RootCNC/Root-2-CNC/STL_Files/X Carriage/X Carraige.png

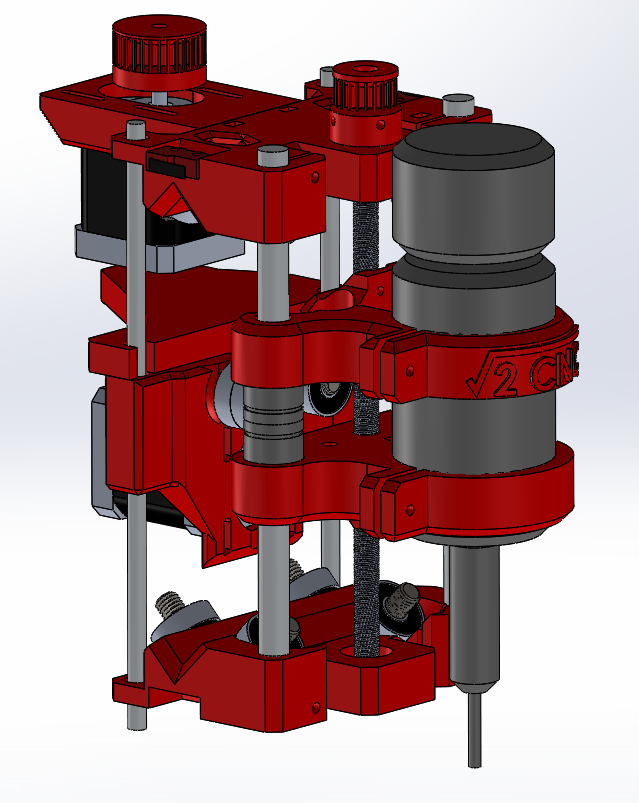
STL_Files/X Carriage/X Carraige.png
