RootCNC/Root-2-CNC/STL_Files/Z Carraige/Spindle Mount.png

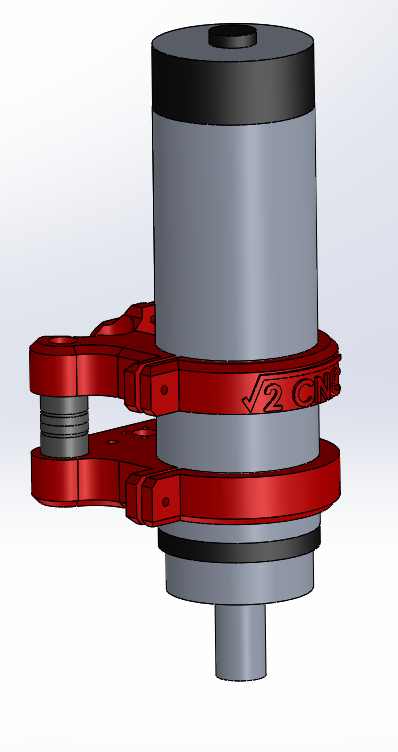
STL_Files/Z Carraige/Spindle Mount.png
