RootCNC/Root-2-CNC/Wooden_Parts/Base Board.png

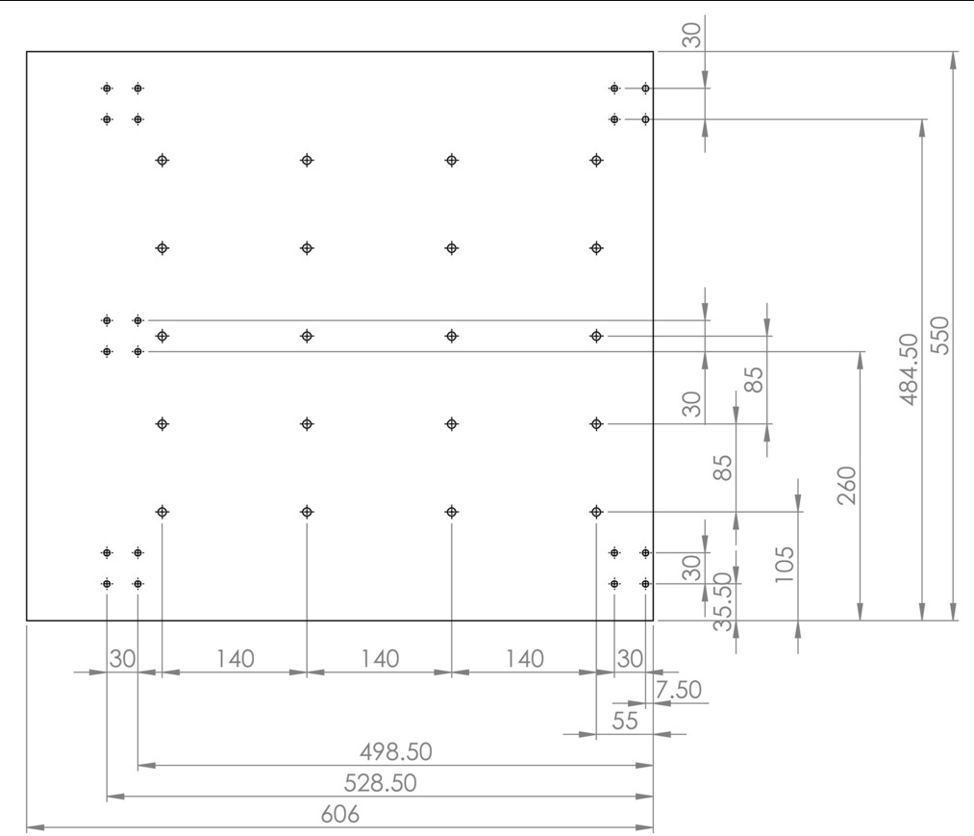
Wooden_Parts/Base Board.png
