RootCNC/Root-2-CNC/Wooden_Parts/Side Panel.png

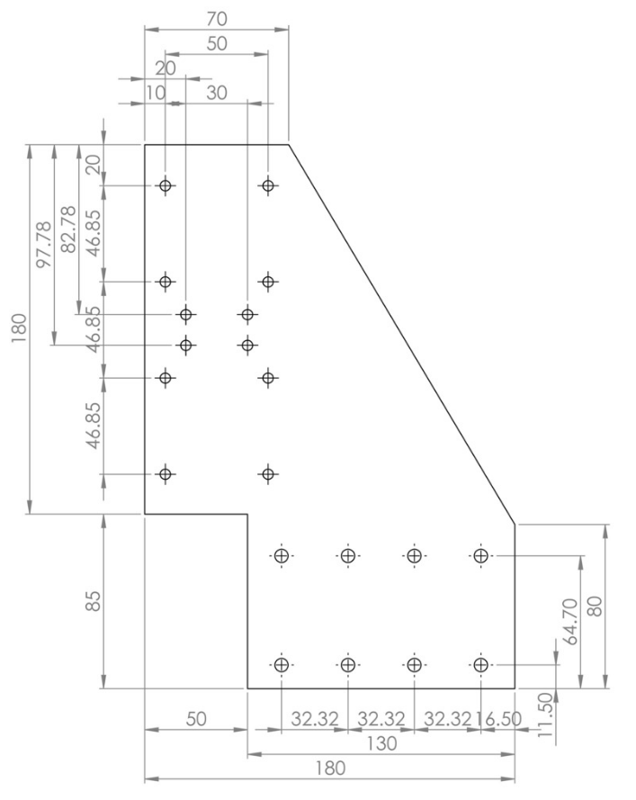
Wooden_Parts/Side Panel.png
