RootCNC/Root-2-CNC/STL_Files/X Carriage/X-Axis Motor Mount.STL

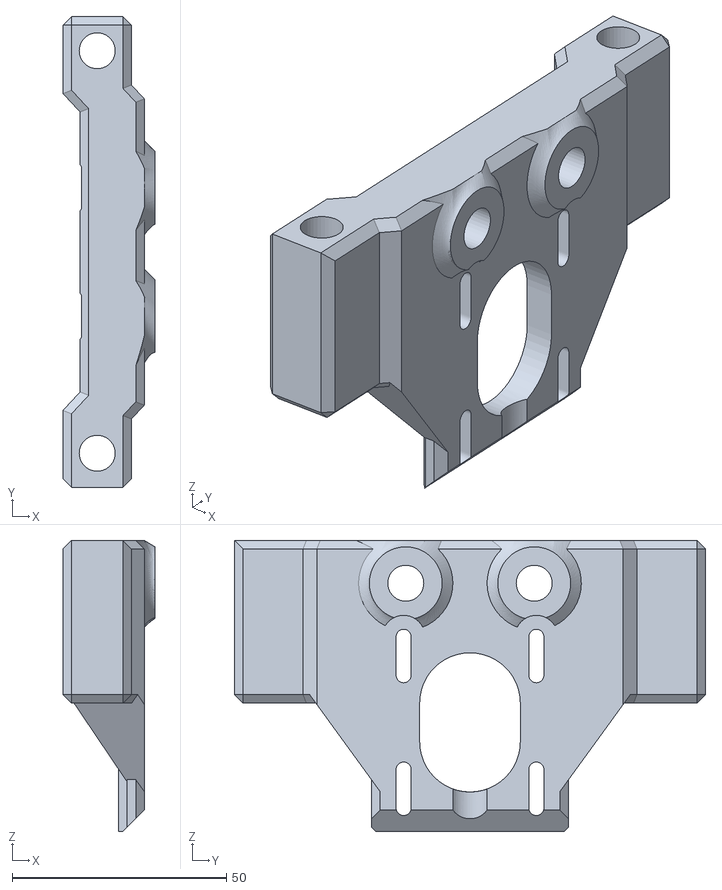
[picture p21: CAD file, 2020-06-19]
STL_Files/X Carriage/X-Axis Motor Mount.STL
21.5 x 110.0 x 68.0
