RootCNC/Root-2-CNC/STL_Files/Y Gantry/X-Axis Belt Clamp.STL

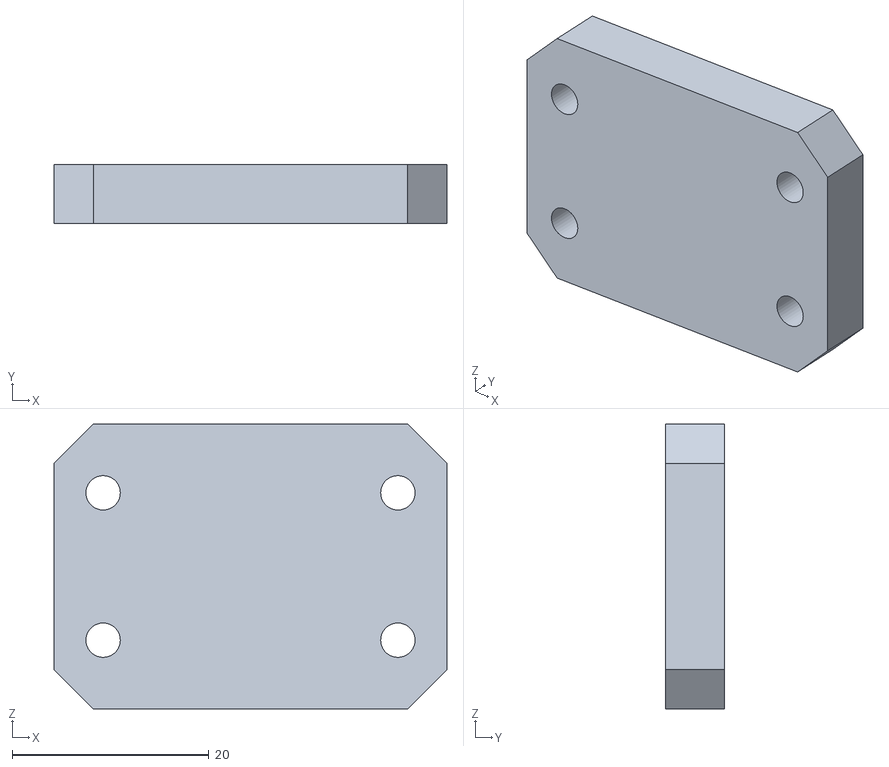
[picture p22: CAD file, 2020-06-19]
STL_Files/Y Gantry/X-Axis Belt Clamp.STL
40.0 x 6.00 x 29.0
