RootCNC/Root-2-CNC/STL_Files/Y Motion/Foot.STL

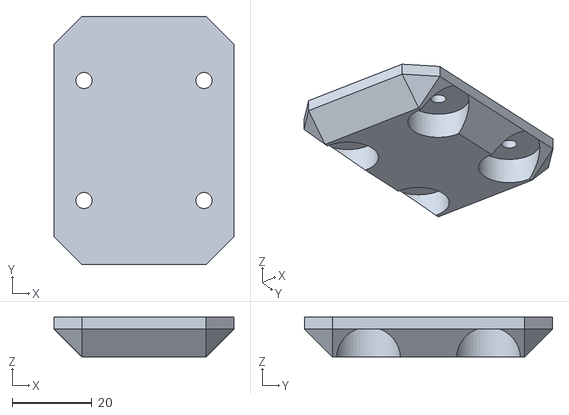
[picture p23: CAD file, 2020-06-19]
STL_Files/Y Motion/Foot.STL
45.0 x 62.0 x 10.0
