RootCNC/Root-2-CNC/STL_Files/Y Motion/INCHES 1'/Root 2 CNC - Base and Y axis assm-1 Y-Axis Bar Mount Idler INCHES.STL

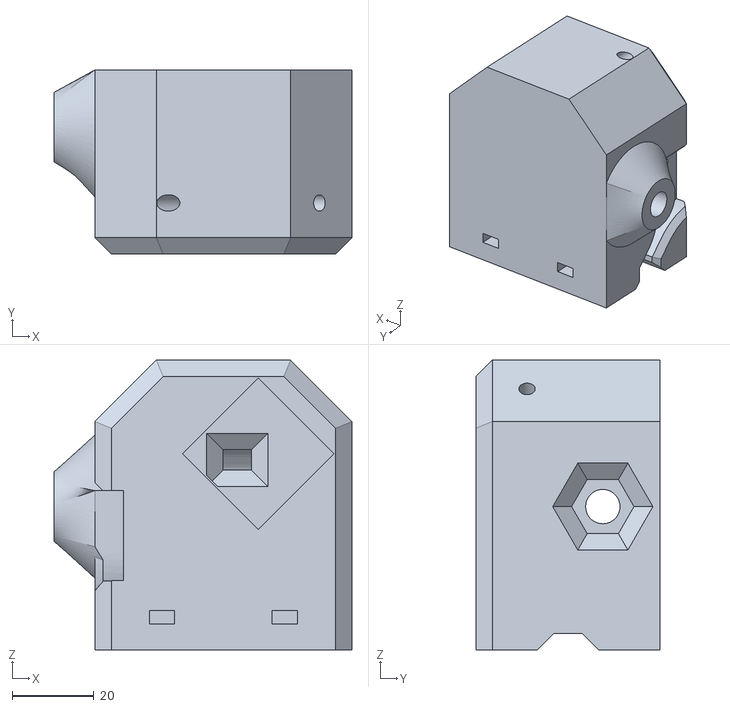
[picture p24: CAD file, 2020-06-19]
STL_Files/Y Motion/INCHES 1'/Root 2 CNC - Base and Y axis assm-1 Y-Axis Bar Mount Idler INCHES.STL
72.8 x 45.0 x 70.8
