RootCNC/Root-2-CNC/STL_Files/Z Carraige/52mm/Spindle Clamp 52mm Top.STL

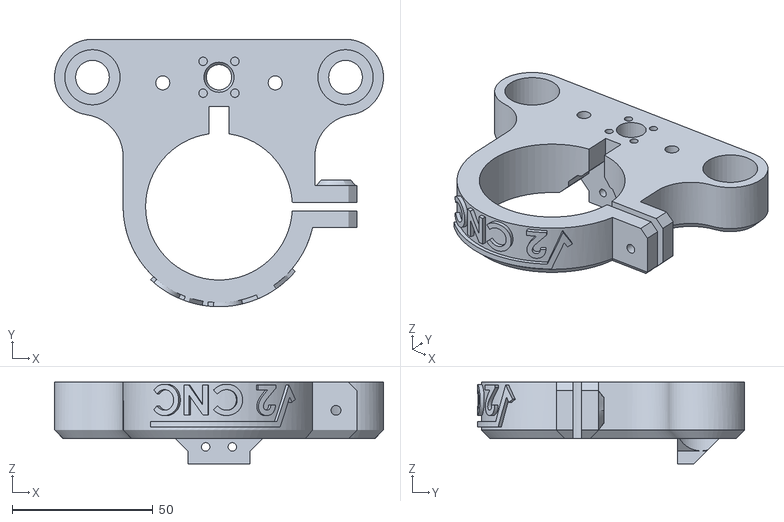
[picture p25: CAD file, 2020-06-19]
STL_Files/Z Carraige/52mm/Spindle Clamp 52mm Top.STL
117.0 x 95.1 x 29.0
