RootCNC/Root-2-CNC/STL_Files/Z Carraige/80mm/Spindle Clamp 80mm Bottom.STL

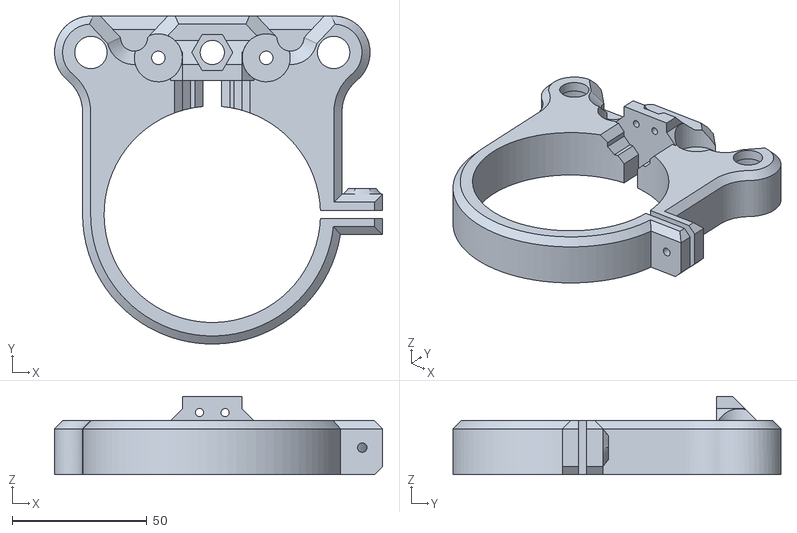
[picture p26: CAD file, 2020-06-19]
STL_Files/Z Carraige/80mm/Spindle Clamp 80mm Bottom.STL
121.6 x 121.6 x 29.0
