RootCNC/Root-2-CNC/Wooden_Parts/X-Axis Side Pannel (Wood).STL

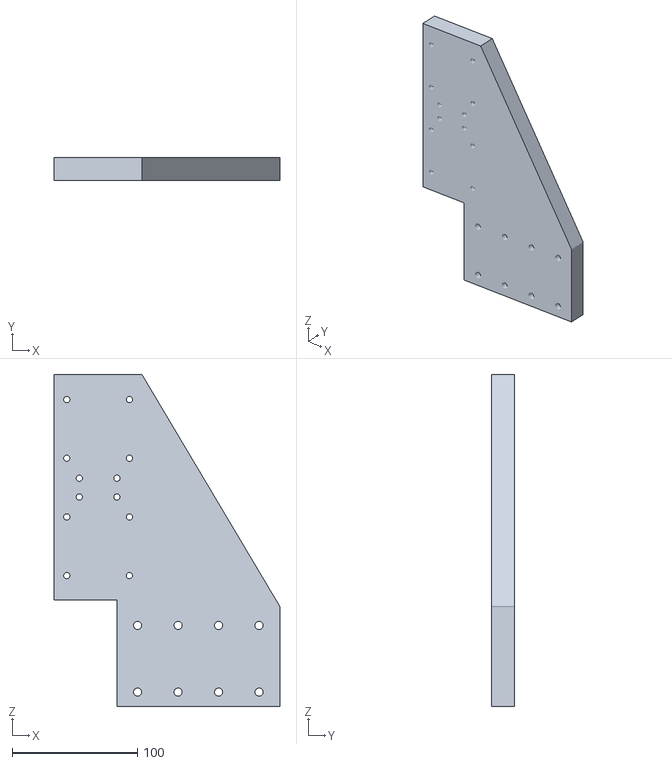
[picture p27: CAD file, 2020-06-19]
Wooden_Parts/X-Axis Side Pannel (Wood).STL
180.0 x 18.0 x 265.0
