RootCNC/Root-2-CNC/STL_Files/X Carriage/X-Axis Carriage Drag Chain Mount Idler.STL

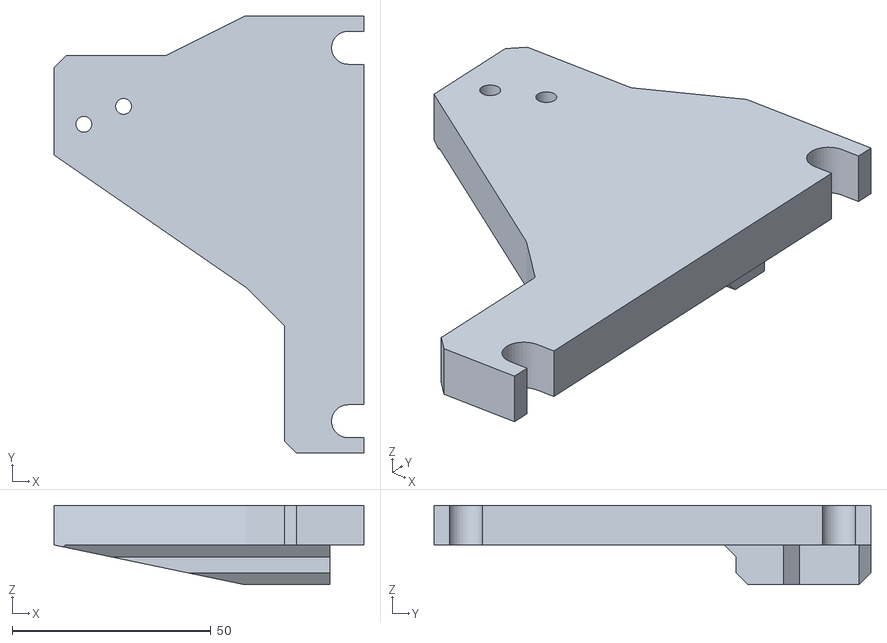
[picture p28: CAD file, 2020-06-19]
STL_Files/X Carriage/X-Axis Carriage Drag Chain Mount Idler.STL
78.0 x 110.0 x 20.0
