RootCNC/Root-2-CNC/STL_Files/Y Gantry/Y-Axis Belt Clamp GT2.STL

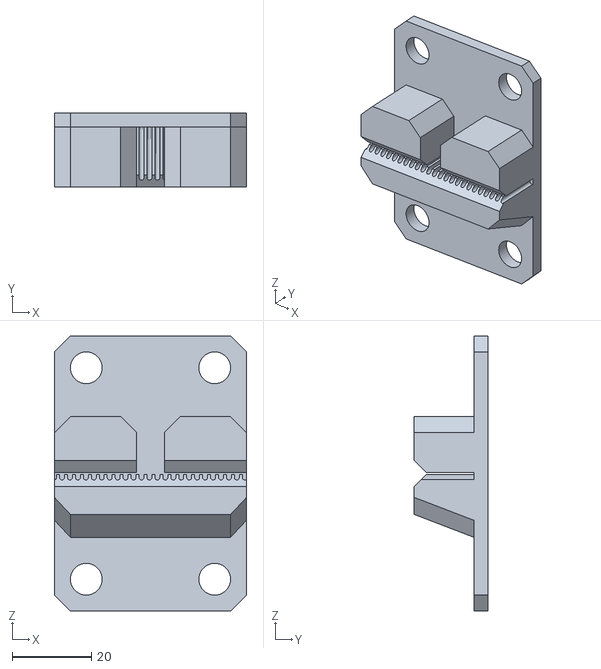
[picture p29: CAD file, 2020-06-19]
STL_Files/Y Gantry/Y-Axis Belt Clamp GT2.STL
48.3 x 18.5 x 69.2
