RootCNC/Root-2-CNC/STL_Files/Y Motion/Y-Axis Motor Mount Mirror.STL

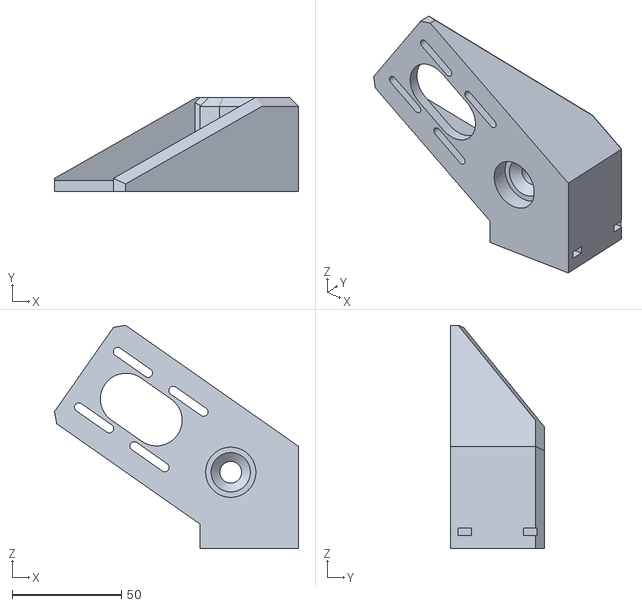
[picture p30: CAD file, 2020-06-19]
STL_Files/Y Motion/Y-Axis Motor Mount Mirror.STL
111.6 x 43.0 x 102.3
