RootCNC/Root-2-CNC/STL_Files/X Carriage/3M Pulley 32T 5mm.STL

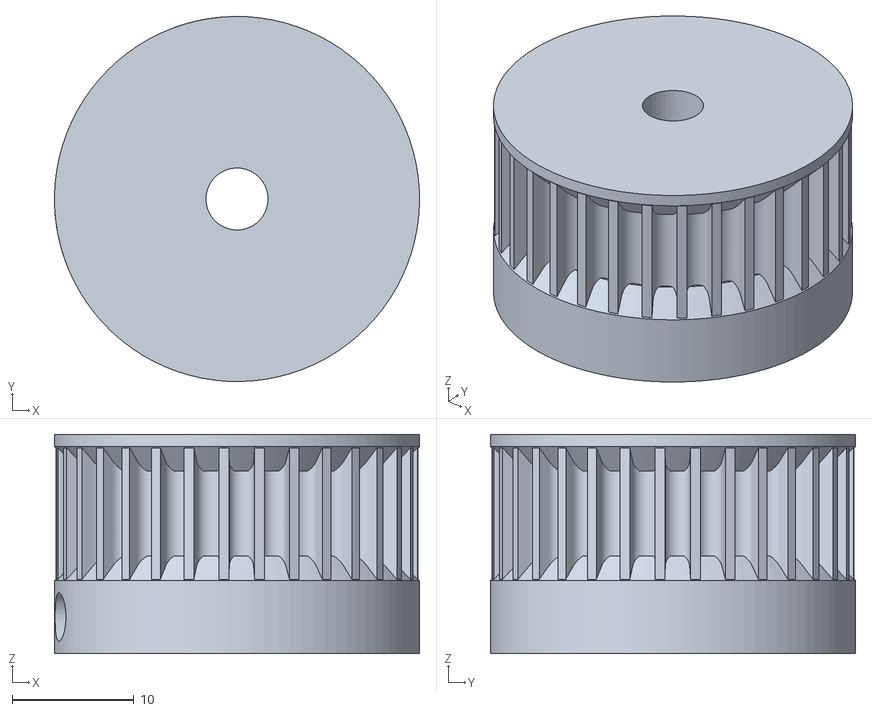
[picture p31: CAD file, 2020-06-19]
STL_Files/X Carriage/3M Pulley 32T 5mm.STL
30.0 x 30.0 x 18.0
