RootCNC/Root-2-CNC/STL_Files/Y Motion/3M Pulley 48T 8mm.STL

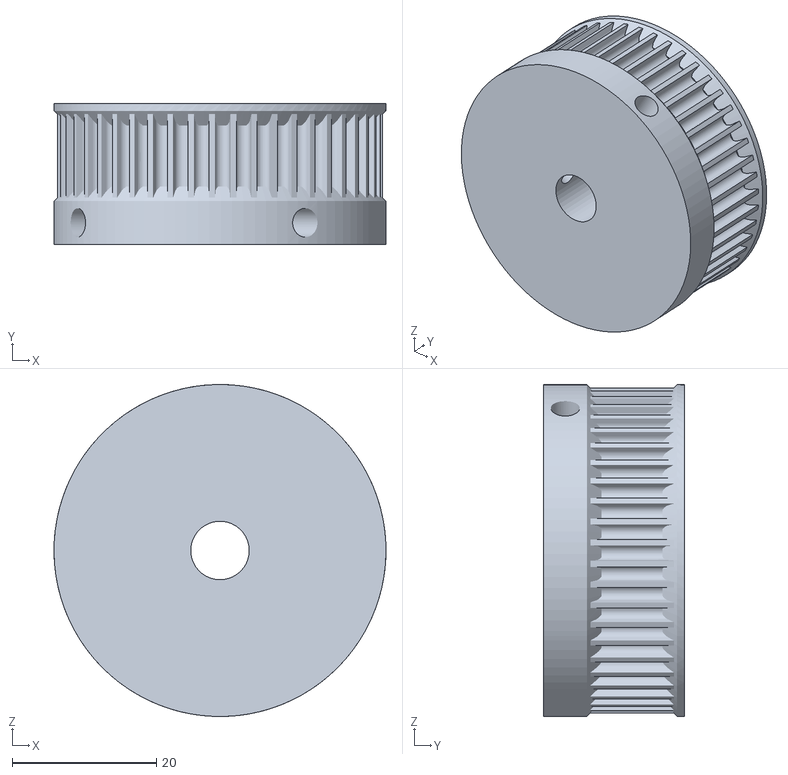
[picture p32: CAD file, 2020-06-19]
STL_Files/Y Motion/3M Pulley 48T 8mm.STL
46.0 x 19.5 x 46.0
