RootCNC/Root-2-CNC/STL_Files/X Carriage/linear rail 90 bearing mount Y-Axis Carriage.STL

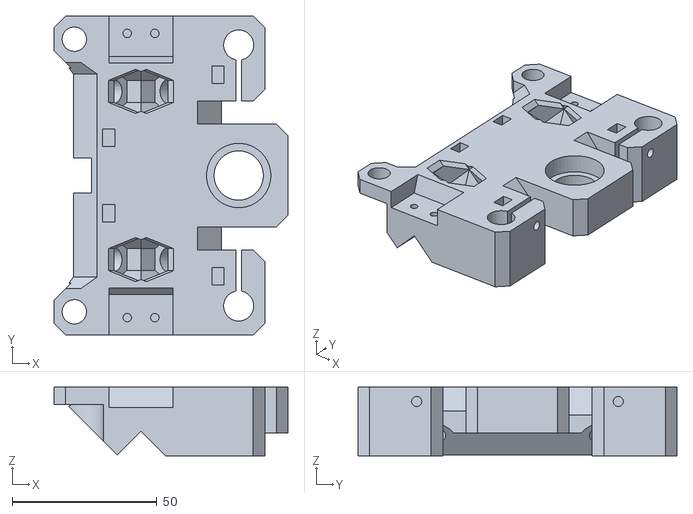
[picture p33: CAD file, 2020-06-19]
STL_Files/X Carriage/linear rail 90 bearing mount Y-Axis Carriage.STL
80.7 x 110.0 x 23.8
