RootCNC/Root-2-CNC/STL_Files/Y Gantry/Dirt Cover.STL

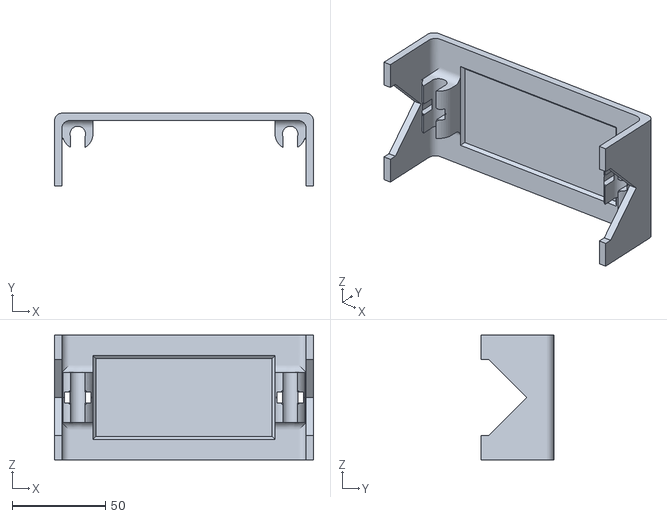
[picture p34: CAD file, 2020-06-19]
STL_Files/Y Gantry/Dirt Cover.STL
139.0 x 39.0 x 67.0
