RootCNC/Root-2-CNC/STL_Files/X Carriage/Z-Axis Motor Mount.STL

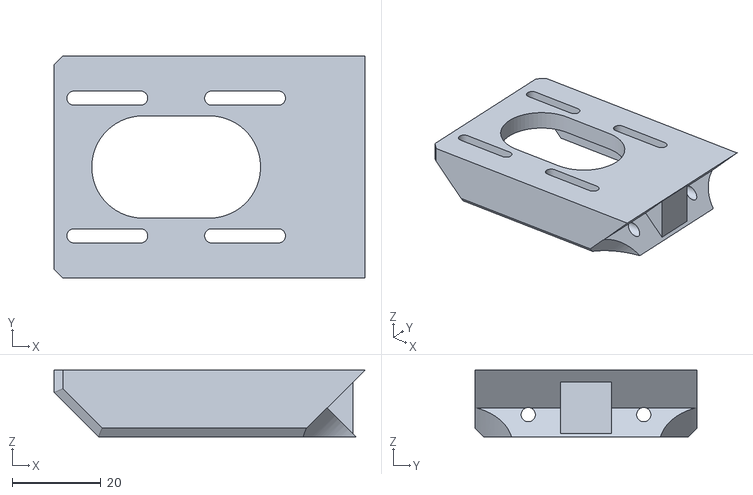
[picture p35: CAD file, 2020-06-19]
STL_Files/X Carriage/Z-Axis Motor Mount.STL
70.0 x 50.0 x 15.0
