RootCNC/Root-2-CNC/STL_Files/Y Motion/Y-Axis Motor Mount NEMA23.STL

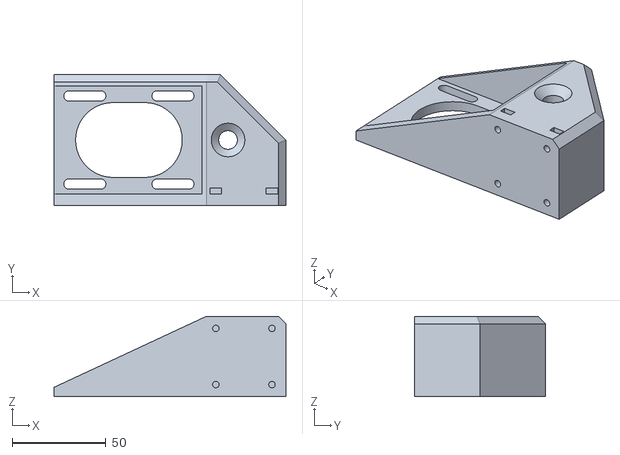
[picture p36: CAD file, 2020-06-19]
STL_Files/Y Motion/Y-Axis Motor Mount NEMA23.STL
124.1 x 70.0 x 43.0
