RootCNC/Root-2-CNC/STL_Files/Y Gantry/Y Motion Bearing Mount.STL

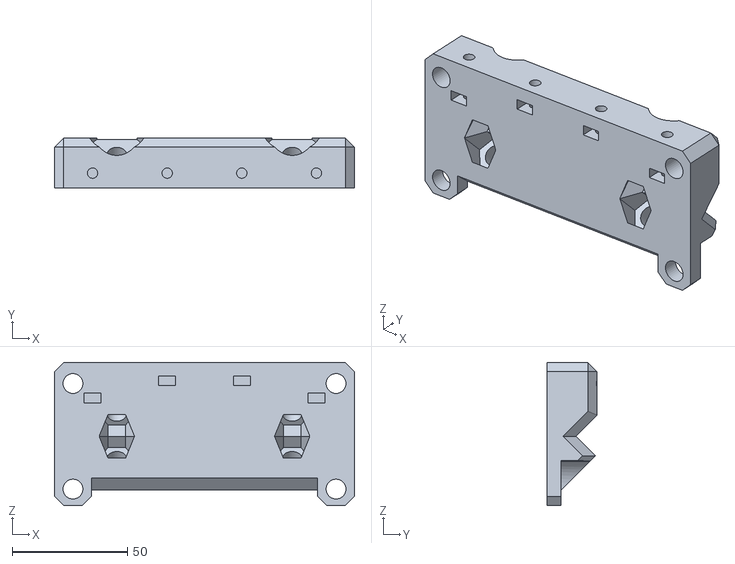
[picture p37: CAD file, 2020-06-19]
STL_Files/Y Gantry/Y Motion Bearing Mount.STL
130.0 x 21.8 x 62.0
