RootCNC/Root-2-CNC/Media/Docs/Build-Images/ex_462df04a4a840081806233b5747140b8_preview_featured.jpg

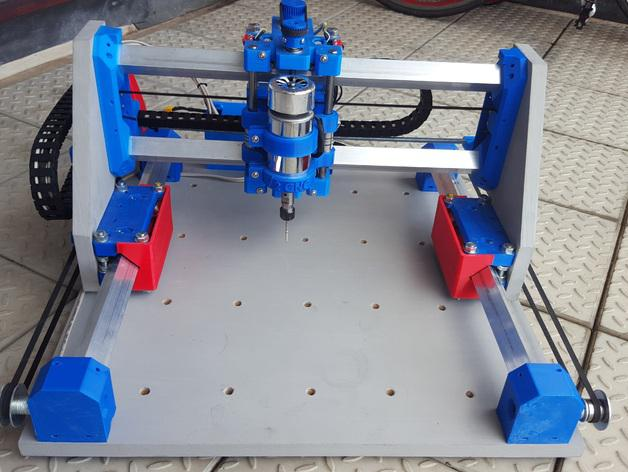
Media/Docs/Build-Images/ex_462df04a4a840081806233b5747140b8_preview_featured.jpg
