RootCNC/Root-2-CNC/Media/Docs/Build-Images/ex_20150905_201603-e1496257583823.jpg

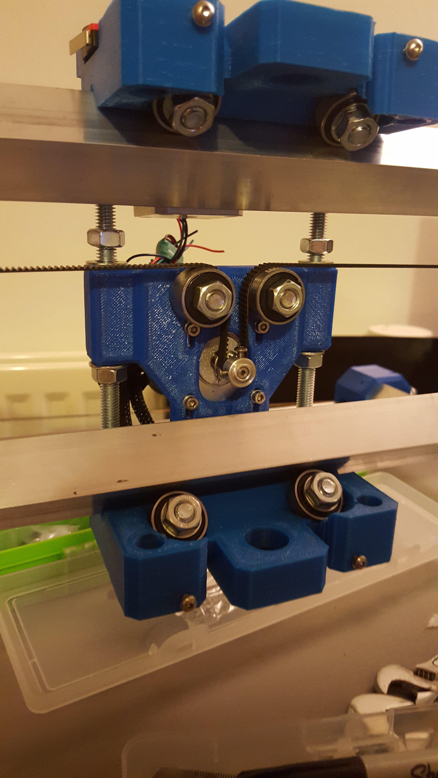
Media/Docs/Build-Images/ex_20150905_201603-e1496257583823.jpg
