RootCNC/Root-2-CNC/Media/Docs/Build-Images/ex_20150905_201616.jpg

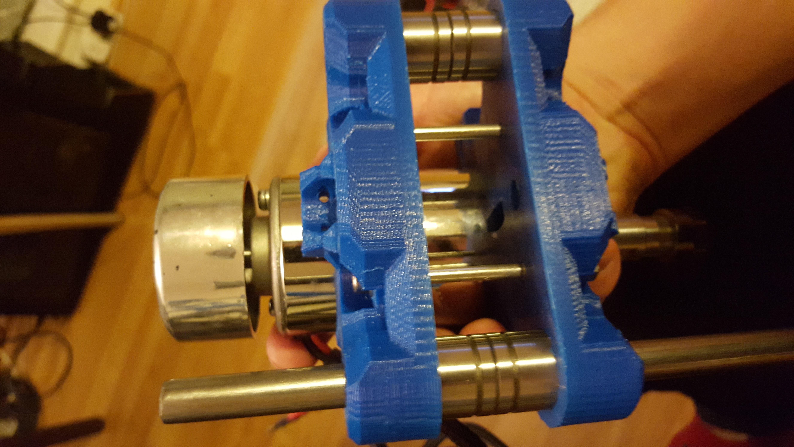
Media/Docs/Build-Images/ex_20150905_201616.jpg
