RootCNC/Root-2-CNC/Media/Docs/Build-Images/ex_20150917_221700.jpg

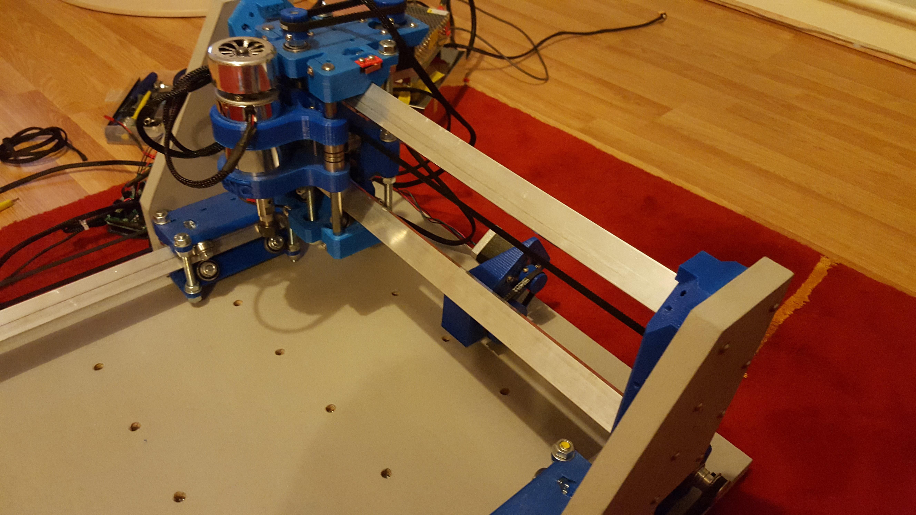
Media/Docs/Build-Images/ex_20150917_221700.jpg
