RootCNC/Root-2-CNC/Media/Docs/Build-Images/ex_20151009_202640.jpg

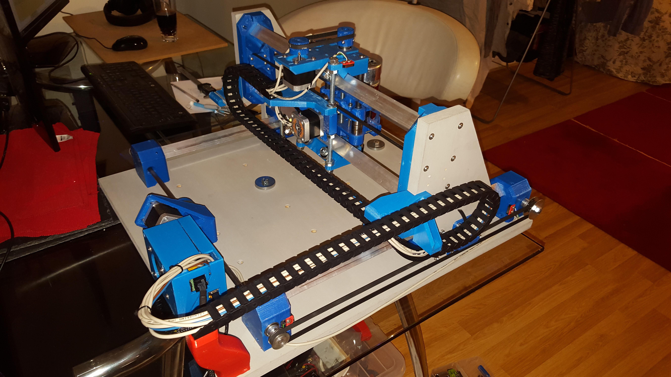
Media/Docs/Build-Images/ex_20151009_202640.jpg
