RootCNC/Root-2-CNC/Media/Docs/Build-Images/ex_20151018_134322-e1496259210734.jpg

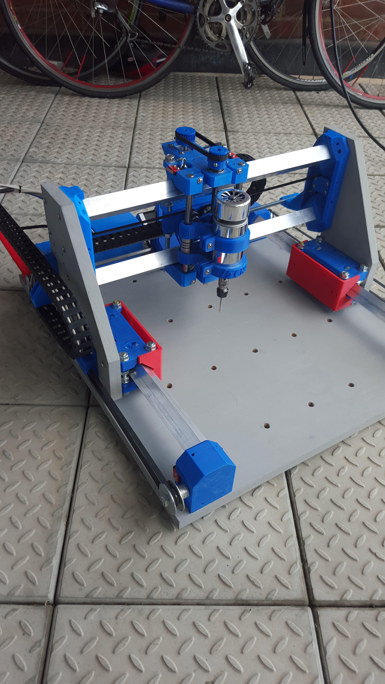
Media/Docs/Build-Images/ex_20151018_134322-e1496259210734.jpg
