RootCNC/Root-2-CNC/Media/Docs/Build-Images/ex_20151018_134347-e1496258479101.jpg

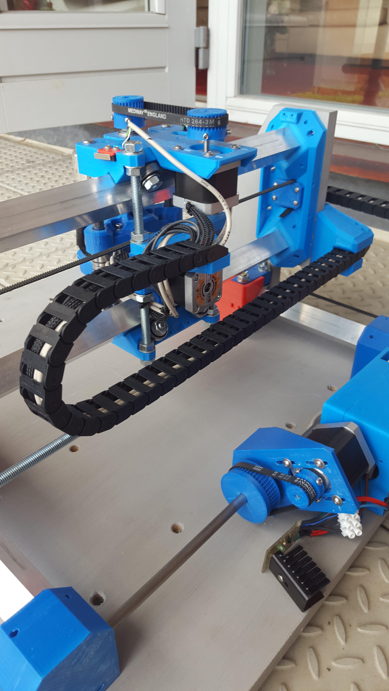
Media/Docs/Build-Images/ex_20151018_134347-e1496258479101.jpg
