RootCNC/Root-2-CNC/Media/Docs/Build-Images/ex_20151018_134348-e1496256414747.jpg

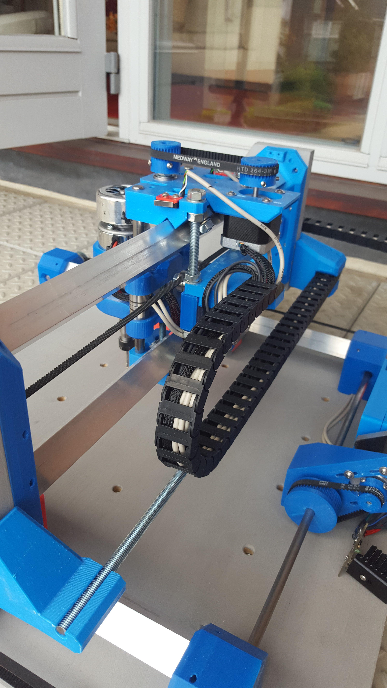
Media/Docs/Build-Images/ex_20151018_134348-e1496256414747.jpg
