RootCNC/Root-2-CNC/Media/Docs/Build-Images/ex_20151018_134350-e1496256656479.jpg

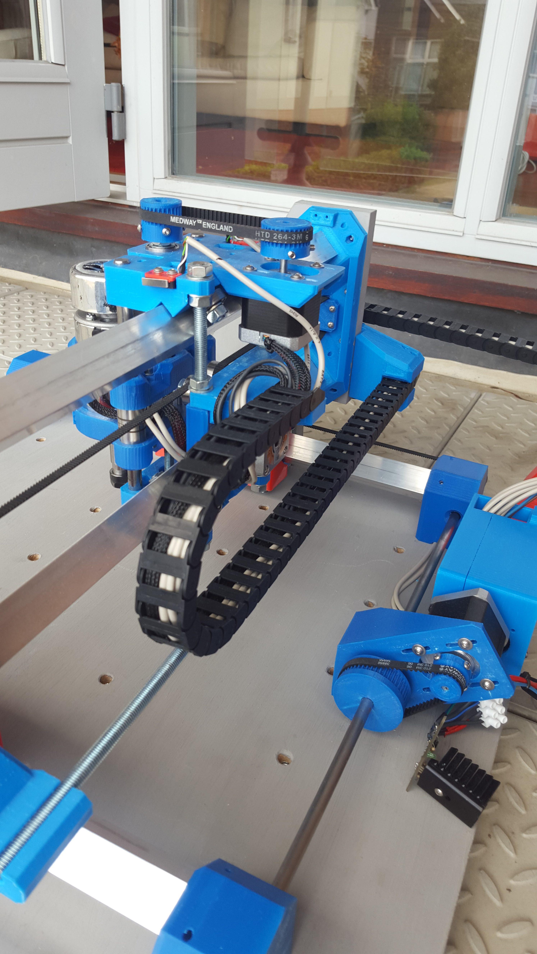
Media/Docs/Build-Images/ex_20151018_134350-e1496256656479.jpg
