RootCNC/Root-2-CNC/Media/Docs/Build-Images/ex_20151018_134354.jpg

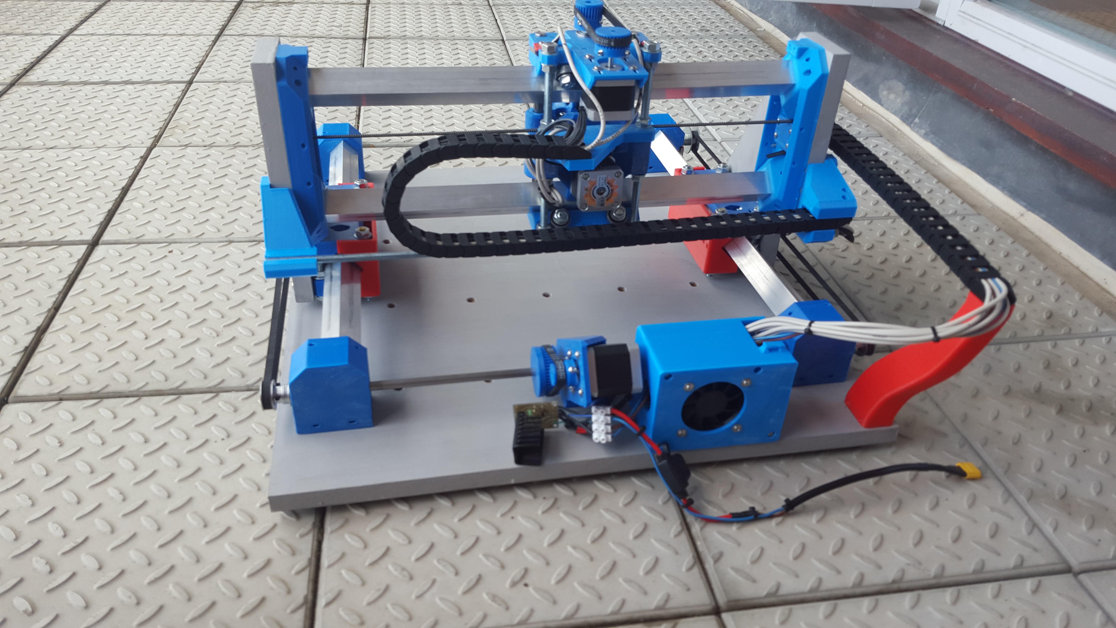
Media/Docs/Build-Images/ex_20151018_134354.jpg
