RootCNC/Root-2-CNC/Media/Docs/Build-Images/ex_20151102_194207.jpg

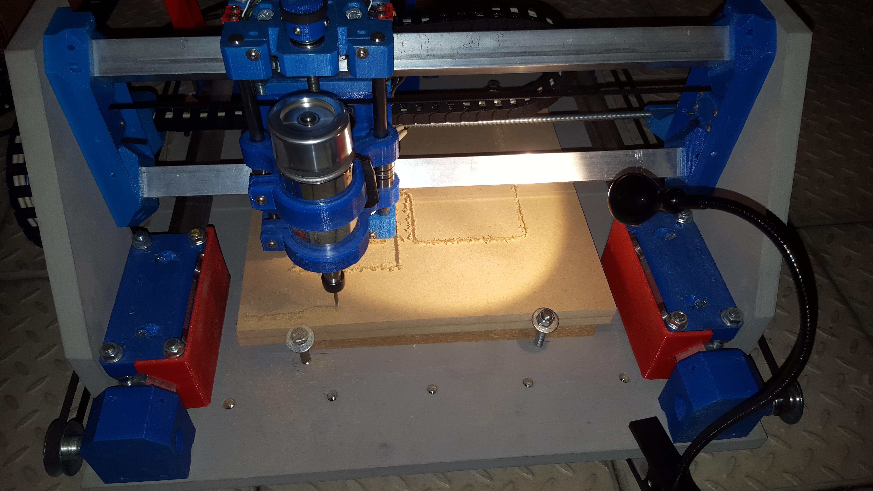
Media/Docs/Build-Images/ex_20151102_194207.jpg
