RootCNC/Root-2-CNC/Media/Docs/Build-Images/ex_20151102_205508.jpg

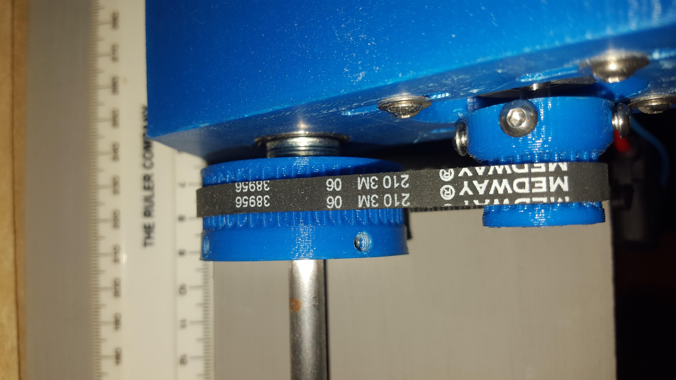
Media/Docs/Build-Images/ex_20151102_205508.jpg
