RootCNC/Root-2-CNC/Media/Docs/Build-Images/ex_20151105_214847-e1496257526713.jpg

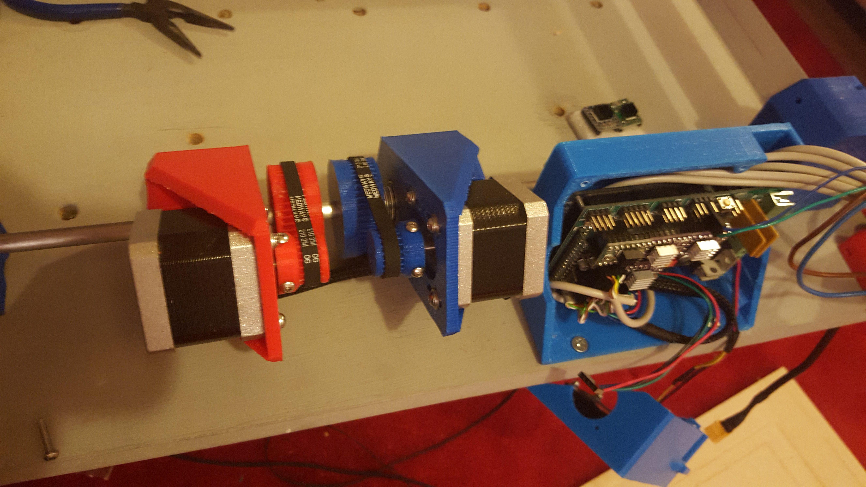
Media/Docs/Build-Images/ex_20151105_214847-e1496257526713.jpg
