RootCNC/Root-2-CNC/Media/Docs/Build-Images/ex_20151105_214853.jpg

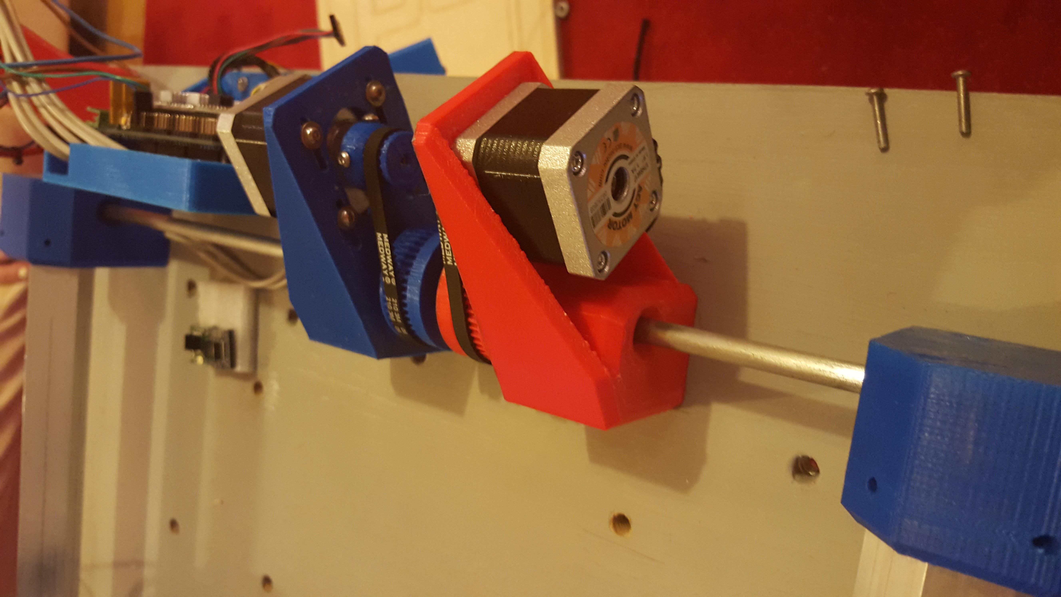
Media/Docs/Build-Images/ex_20151105_214853.jpg
