RootCNC/Root-2-CNC/Media/Docs/Build-Images/ex_20151105_214856.jpg

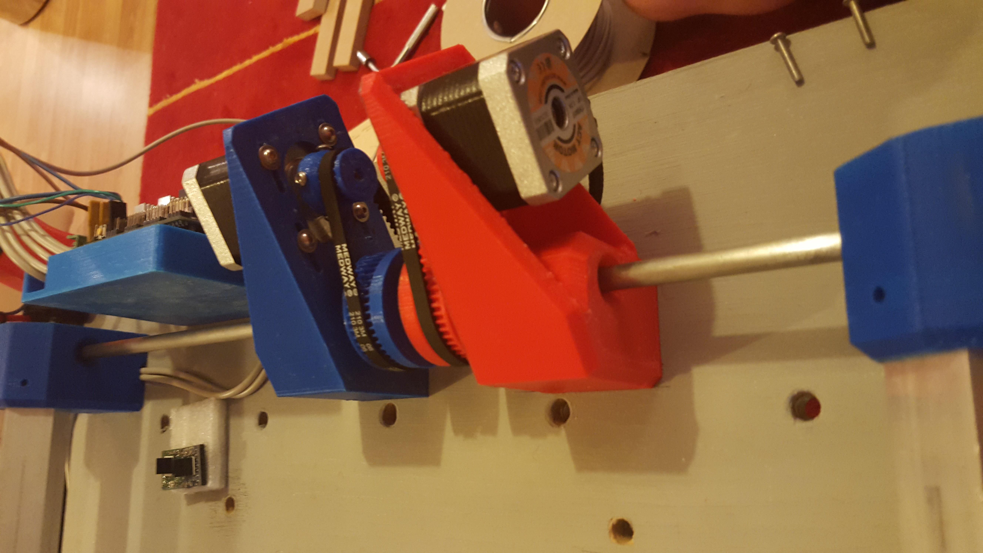
Media/Docs/Build-Images/ex_20151105_214856.jpg
