RootCNC/Root-2-CNC/Media/Docs/Build-Images/ex_20151202_203618-e1496258793423.jpg

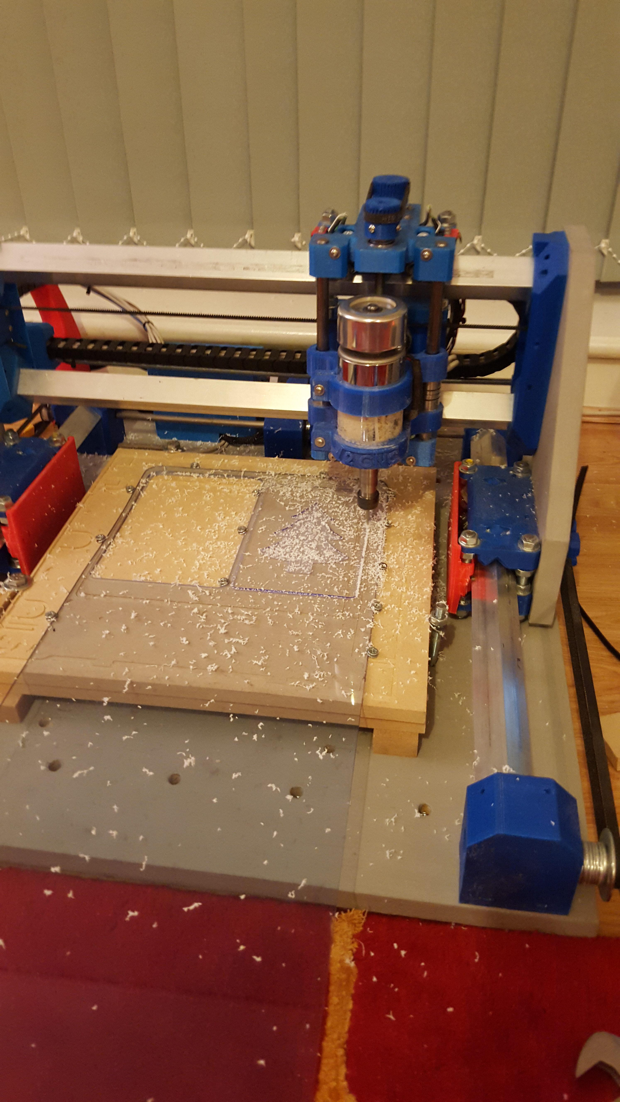
Media/Docs/Build-Images/ex_20151202_203618-e1496258793423.jpg
