RootCNC/Root-2-CNC/Media/Docs/Build-Images/ex_20151202_203644.jpg

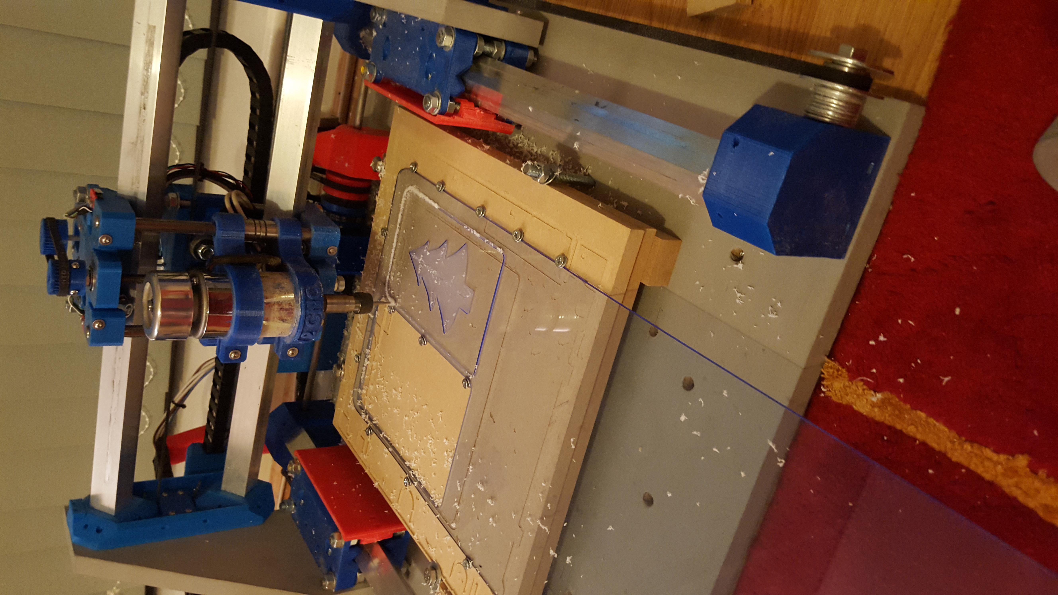
Media/Docs/Build-Images/ex_20151202_203644.jpg
